Ines-chihi3/inertia_wheel_pendulum_labVIEW_ARDUINO/SolidWorks design/BLOCK.SLDPRT

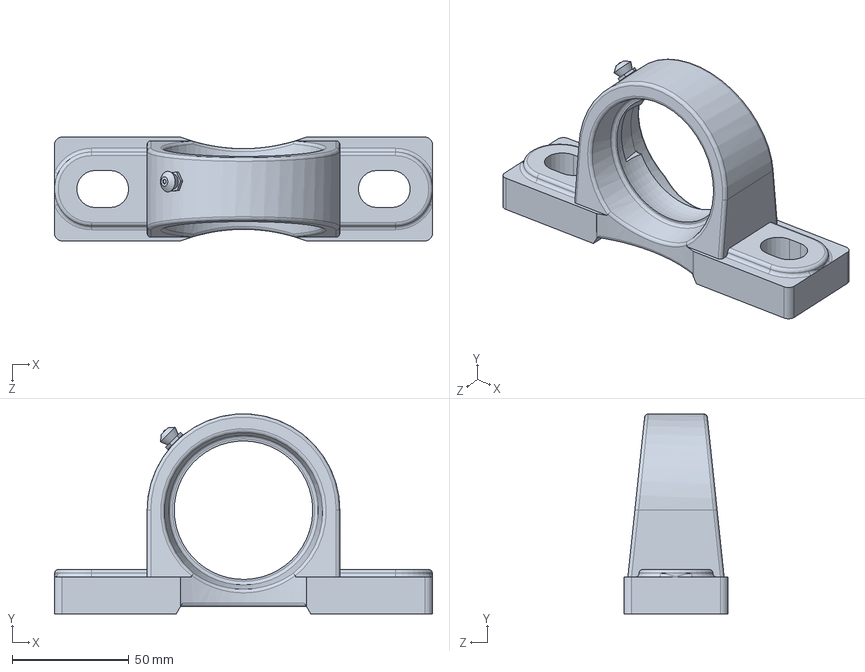
[picture p33: CAD file, 2021-05-16]
SolidWorks design/BLOCK.SLDPRT
161.9 x 85.6 x 44.5 mm
