Ines-chihi3/inertia_wheel_pendulum_labVIEW_ARDUINO/SolidWorks design/Funda de la bateria.SLDPRT

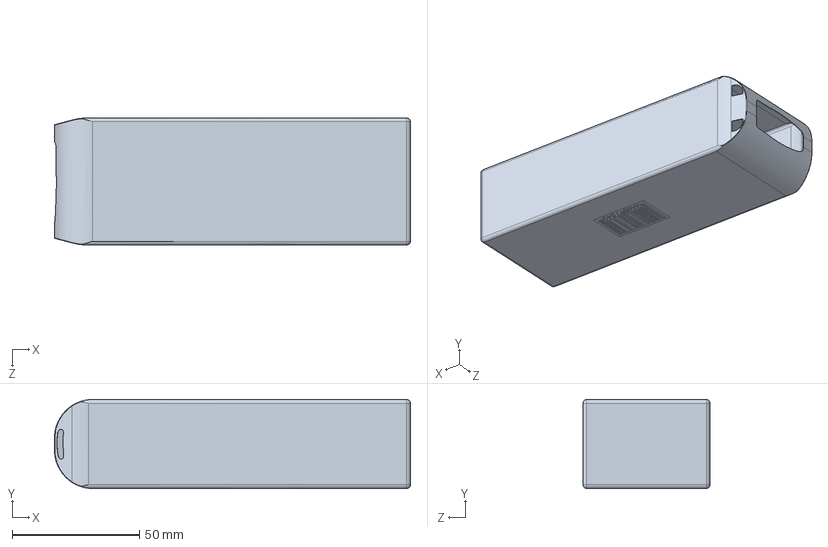
[picture p34: CAD file, 2021-05-16]
SolidWorks design/Funda de la bateria.SLDPRT
140.0 x 35.0 x 50.0 mm
