Ines-chihi3/inertia_wheel_pendulum_labVIEW_ARDUINO/SolidWorks design/JGA25-372 24V Motor.STEP

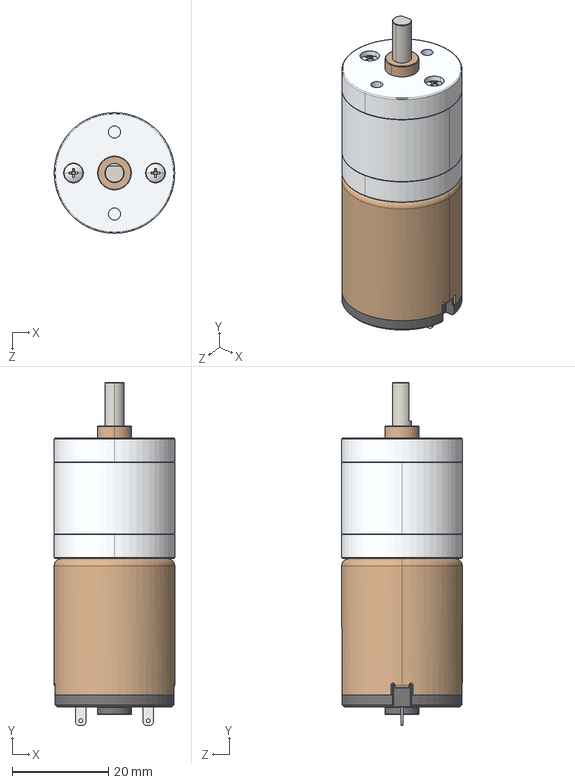
[picture p35: CAD file, 2021-05-16]
SolidWorks design/JGA25-372 24V Motor.STEP
25.0 x 71.1 x 25.0 mm
