Ines-chihi3/inertia_wheel_pendulum_labVIEW_ARDUINO/SolidWorks design/Cytron Motor.STEP

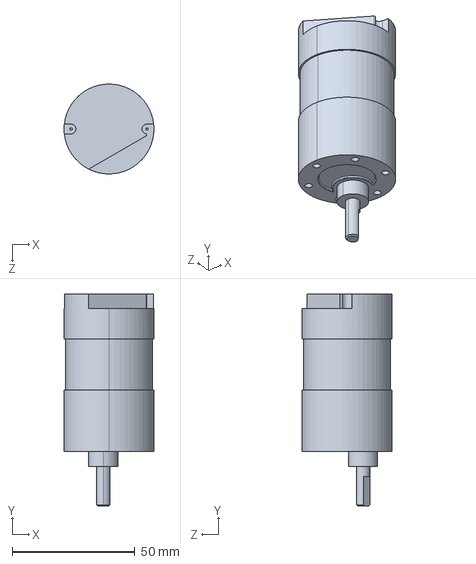
[picture p36: CAD file, 2021-05-16]
SolidWorks design/Cytron Motor.STEP
36.7 x 86.5 x 36.7 mm
