Ines-chihi3/inertia_wheel_pendulum_labVIEW_ARDUINO/SolidWorks design/Conector XT60.SLDPRT

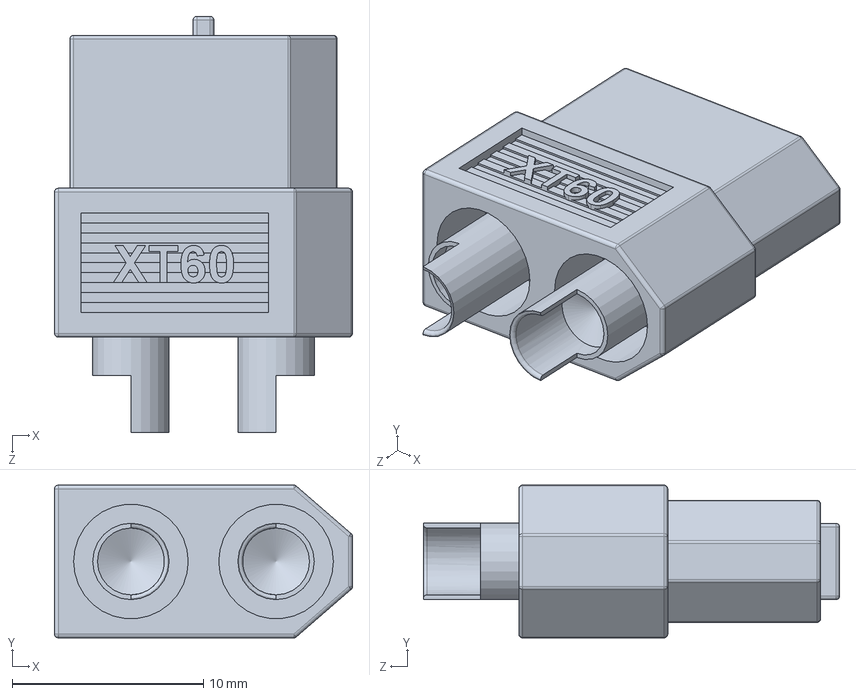
[picture p37: CAD file, 2021-05-16]
SolidWorks design/Conector XT60.SLDPRT
15.6 x 8.00 x 21.8 mm
